mhbleakley/GF24/3D/NX2016SA_NDK.step

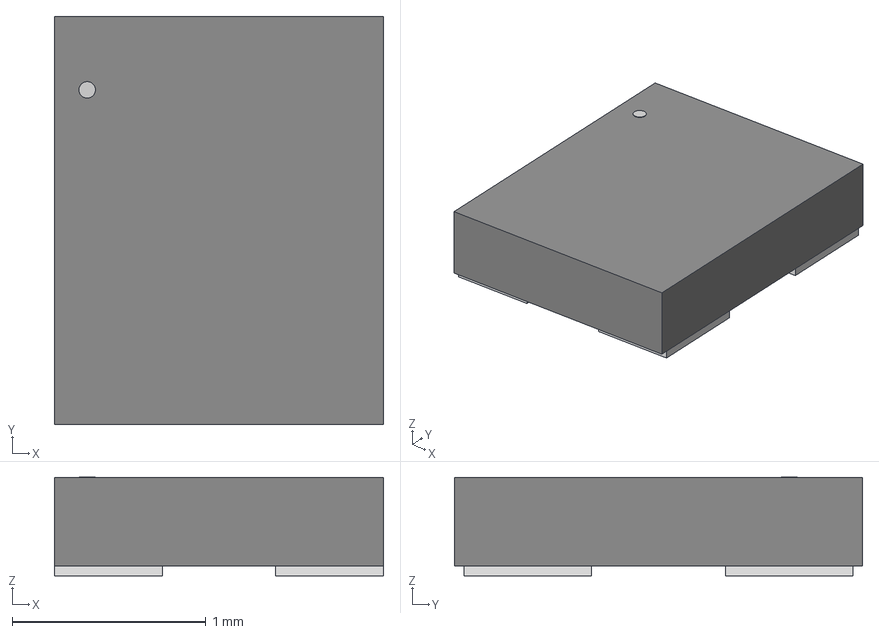
[picture p15: CAD file, 2025-01-12]
3D/NX2016SA_NDK.step
1.70 x 2.11 x 0.511 mm
