mhbleakley/GF24/3D/1101M2S5AQE2.stp

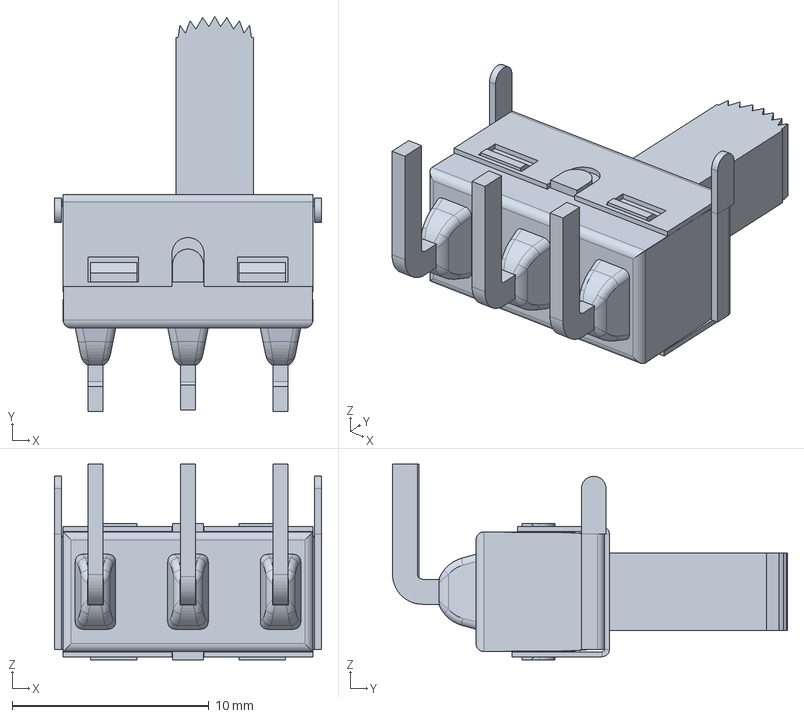
[picture p16: CAD file, 2025-01-12]
3D/1101M2S5AQE2.stp
13.6 x 20.1 x 9.93 mm
