mhbleakley/GF24/3D/3220-10-0100-00--3DModel-STEP-56544.STEP

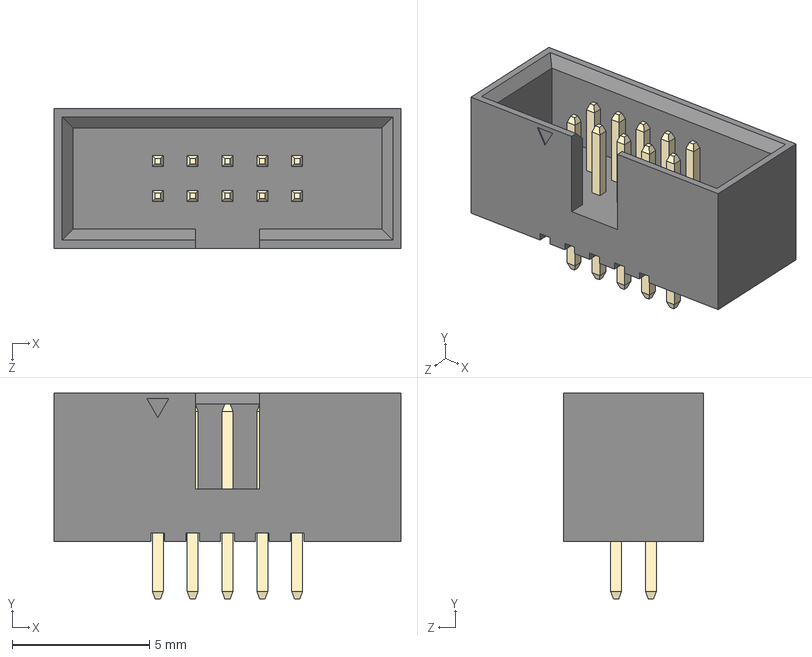
[picture p17: CAD file, 2025-01-12]
3D/3220-10-0100-00--3DModel-STEP-56544.STEP
12.7 x 7.50 x 5.10 mm
3220-xx-0100-00 body_10
Pin^3220-xx-0100-00 x 10
