mhbleakley/GF24/3D/PTS815SJM250SMTRLFS.stp

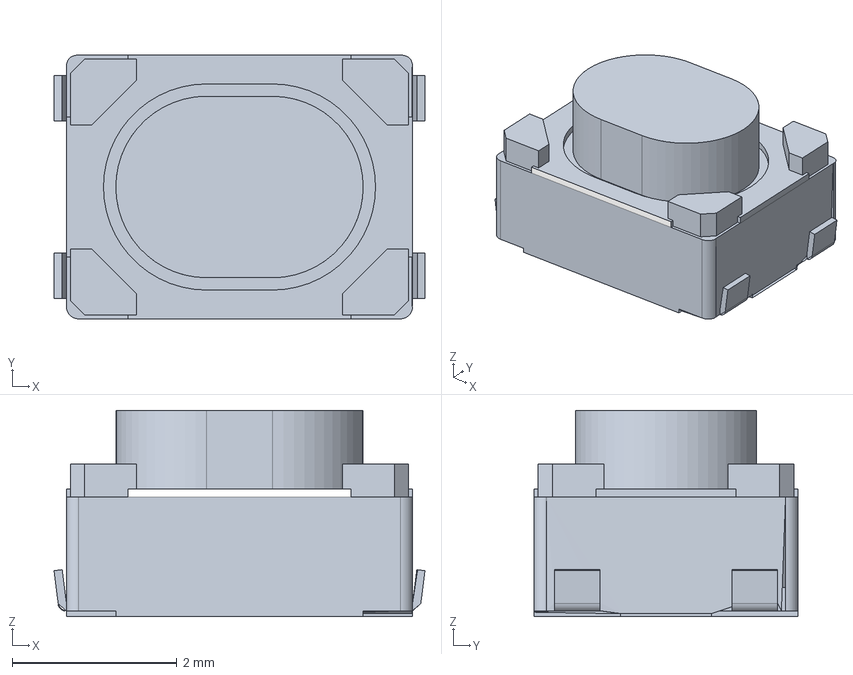
[picture p18: CAD file, 2025-01-12]
3D/PTS815SJM250SMTRLFS.stp
4.50 x 3.20 x 2.50 mm
PTS815SJM250SMTRLFS_PART1
PTS815SJM250SMTRLFS_PART2
PTS815SJM250SMTRLFS_PART3
