mhbleakley/GF24/3D/CJS-1200TA.step

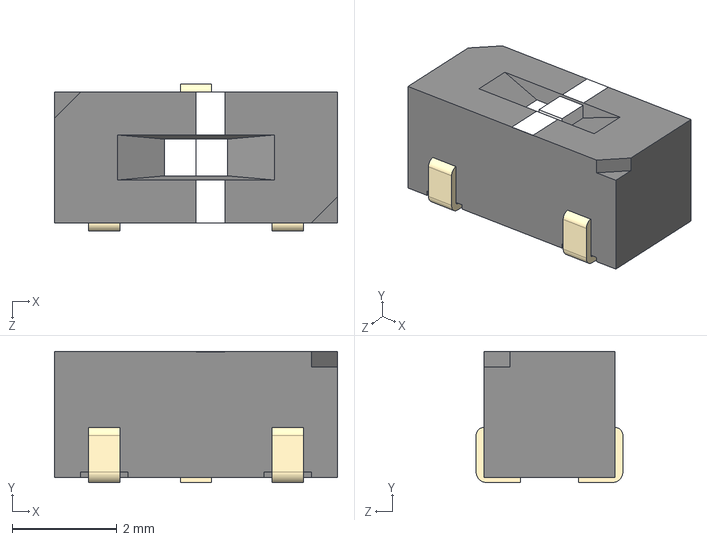
[picture p19: CAD file, 2025-01-12]
3D/CJS-1200TA.step
5.40 x 2.50 x 2.80 mm
