mhbleakley/GF24/3D/RC0603FR-0710KL.STEP

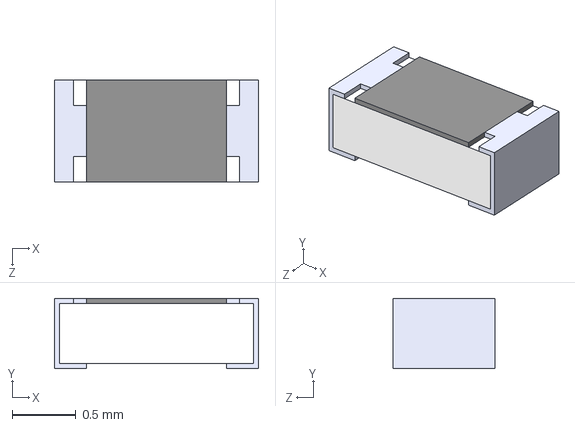
[picture p20: CAD file, 2025-01-12]
3D/RC0603FR-0710KL.STEP
1.60 x 0.55 x 0.8 mm
