mhbleakley/GF24/3D/SAM-M8Q-0.STEP

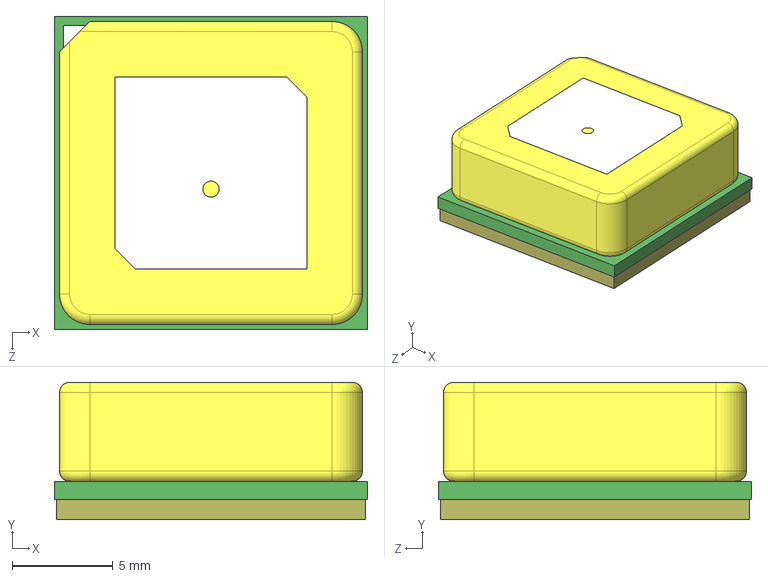
[picture p21: CAD file, 2025-01-12]
3D/SAM-M8Q-0.STEP
15.5 x 6.80 x 15.5 mm
