mhbleakley/GF24/3D/C0402C103K9RACTU.STEP

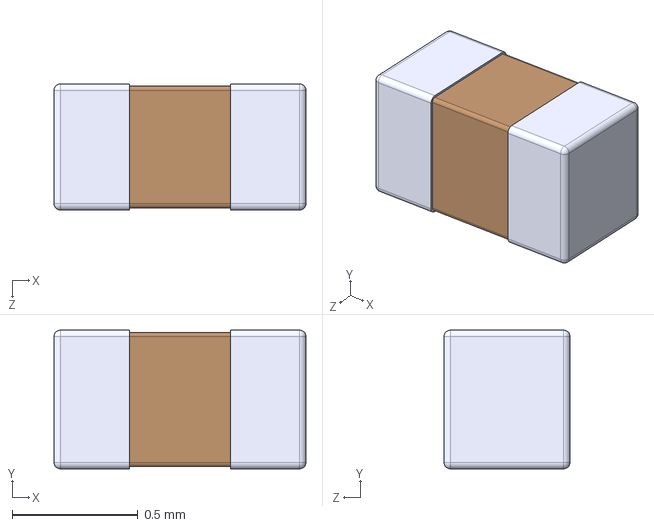
[picture p22: CAD file, 2025-01-12]
3D/C0402C103K9RACTU.STEP
1.00 x 0.55 x 0.5 mm
