mhbleakley/GF24/3D/MMSD4148T1G.STEP

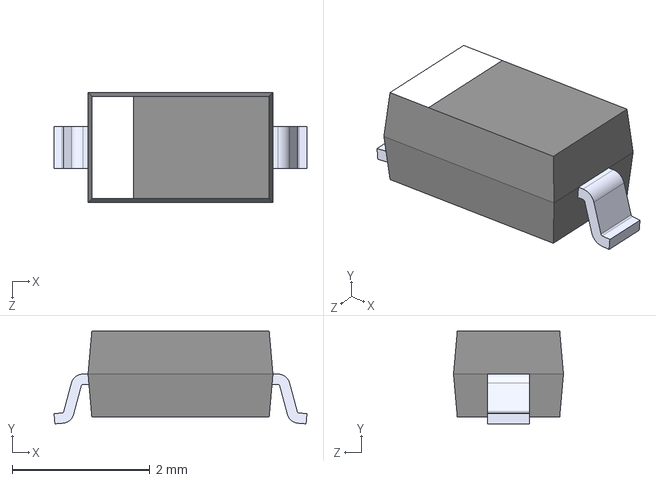
[picture p24: CAD file, 2025-01-12]
3D/MMSD4148T1G.STEP
3.68 x 1.35 x 1.60 mm
