mhbleakley/GF24/3D/CSQG703BP.step

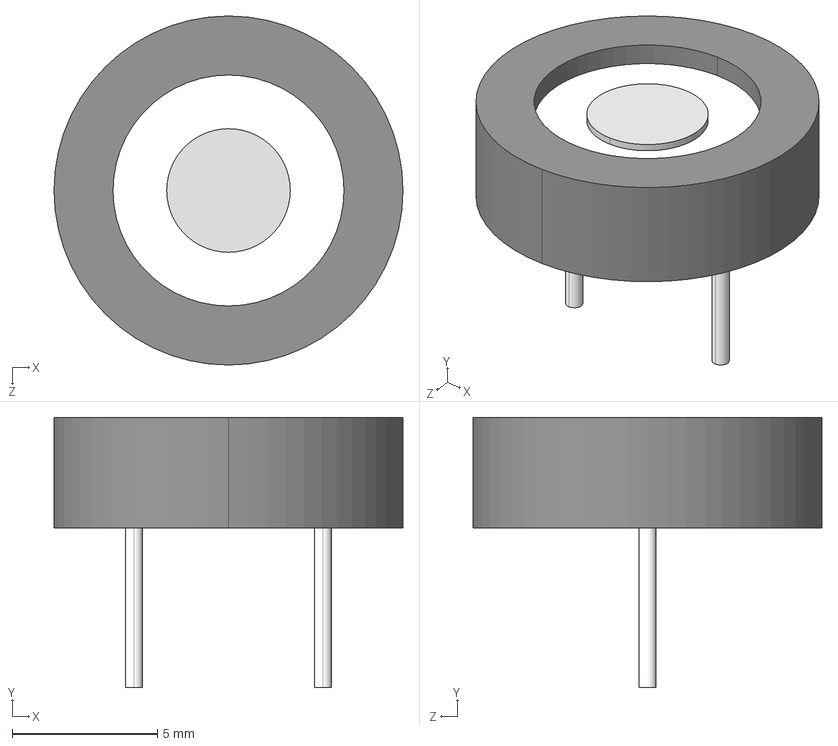
[picture p25: CAD file, 2025-01-12]
3D/CSQG703BP.step
12.0 x 9.30 x 12.0 mm
