mhbleakley/GF24/3D/APBDA3020.STEP

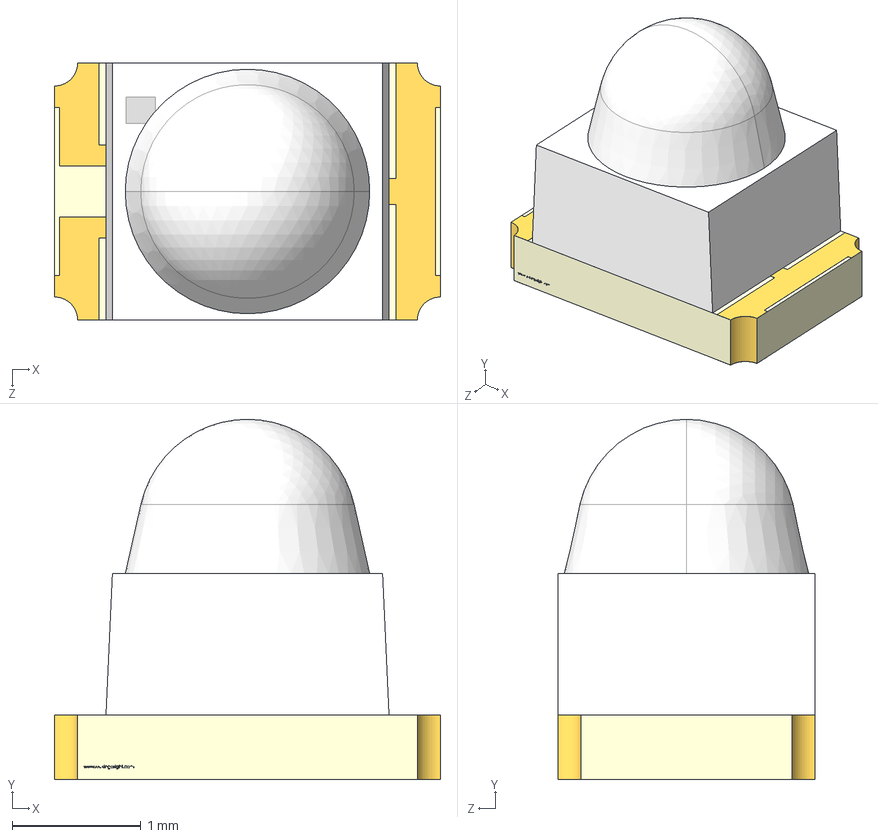
[picture p26: CAD file, 2025-01-12]
3D/APBDA3020.STEP
3.00 x 2.80 x 2.00 mm
