mhbleakley/GF24/3D/LM3671MF-3.3.step

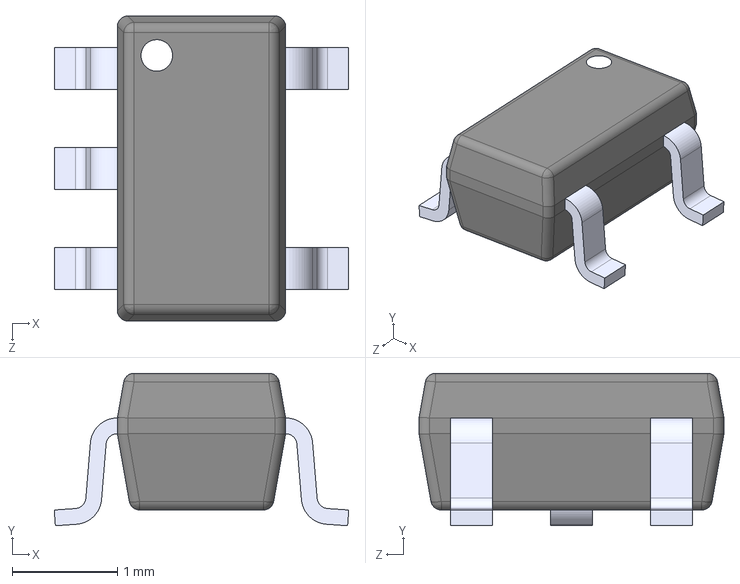
[picture p27: CAD file, 2024-12-28]
3D/LM3671MF-3.3.step
2.80 x 1.45 x 2.90 mm
