mhbleakley/GF24/3D/54.STEP

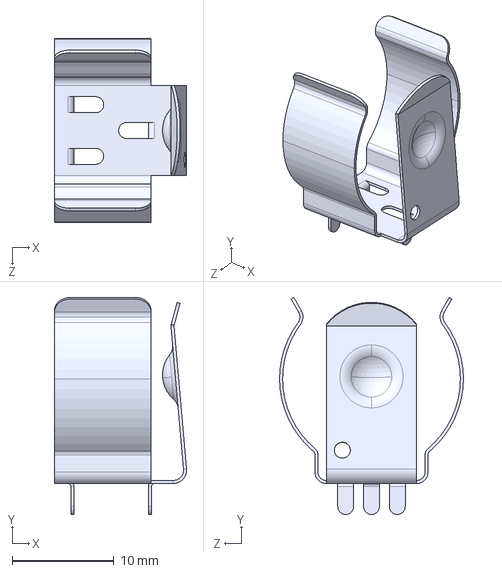
[picture p28: CAD file, 2024-12-27]
3D/54.STEP
13.0 x 21.4 x 18.1 mm
