mhbleakley/GF24/3D/C0603C103K9RACTU.STEP

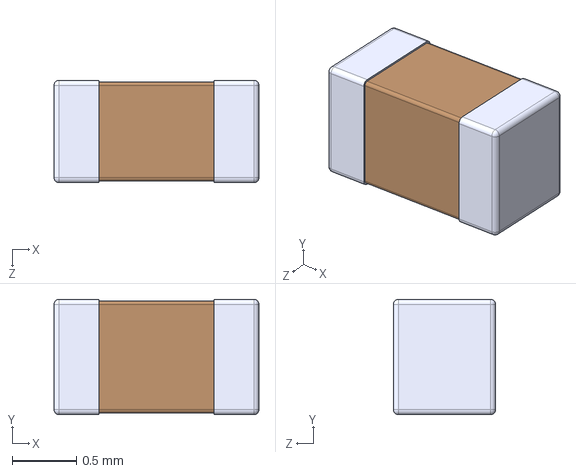
[picture p29: CAD file, 2024-12-27]
3D/C0603C103K9RACTU.STEP
1.60 x 0.9 x 0.8 mm
