mhbleakley/GF24/3D/C1206C475K9RACTU.step

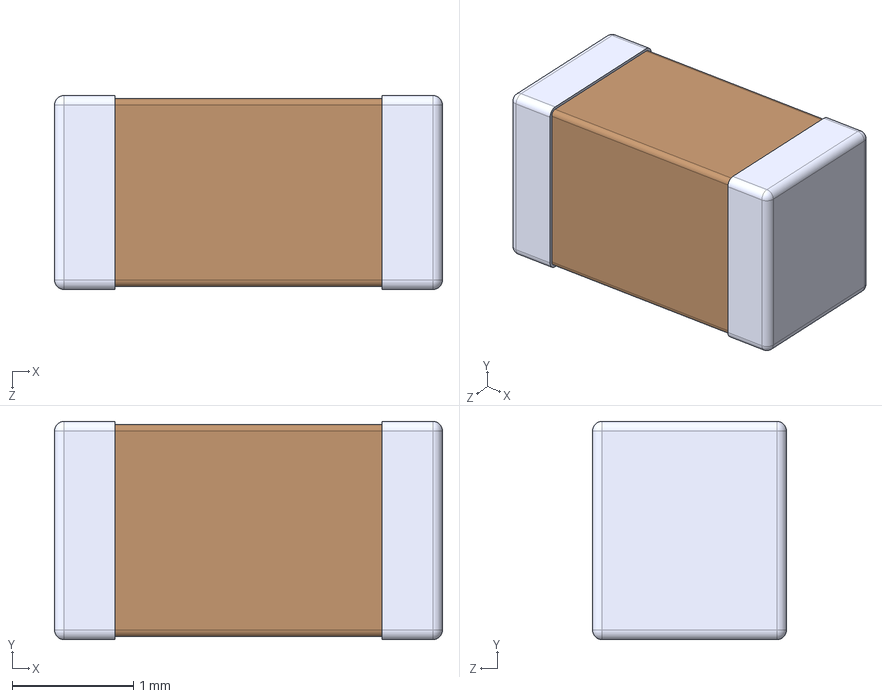
[picture p30: CAD file, 2024-12-27]
3D/C1206C475K9RACTU.step
3.20 x 1.80 x 1.60 mm
