mhbleakley/GF24/3D/RC1206JR-1010KL.step

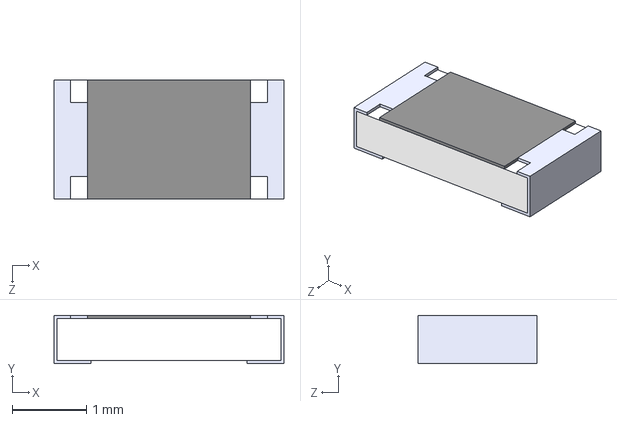
[picture p31: CAD file, 2024-12-27]
3D/RC1206JR-1010KL.step
3.10 x 0.65 x 1.60 mm
