mhbleakley/GF24/3D/C0805C104K9RACTU.step

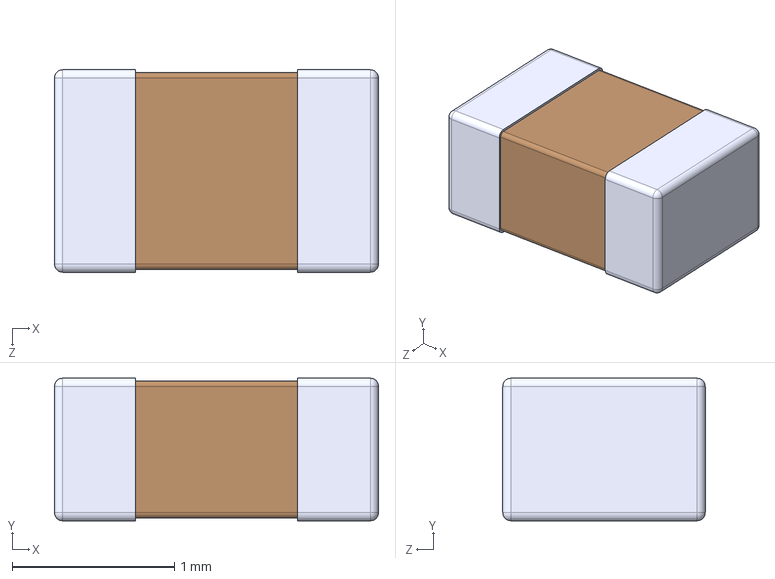
[picture p32: CAD file, 2024-12-27]
3D/C0805C104K9RACTU.step
2.00 x 0.88 x 1.25 mm
