mhbleakley/GF24/3D/ETQ-P3M2R2HFP.STEP

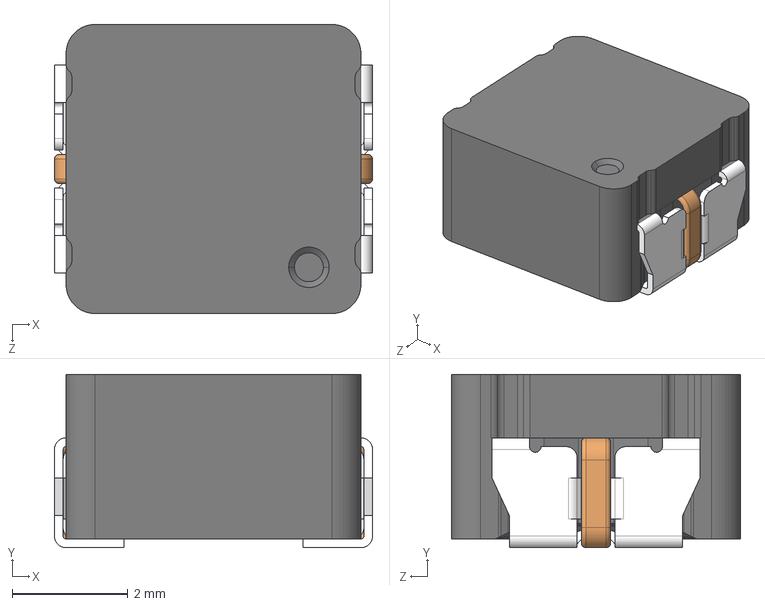
[picture p33: CAD file, 2024-12-27]
3D/ETQ-P3M2R2HFP.STEP
5.50 x 3.00 x 5.00 mm
