mhbleakley/GF24/3D/MAX-M10S-00B--3DModel-STEP-269445.STEP

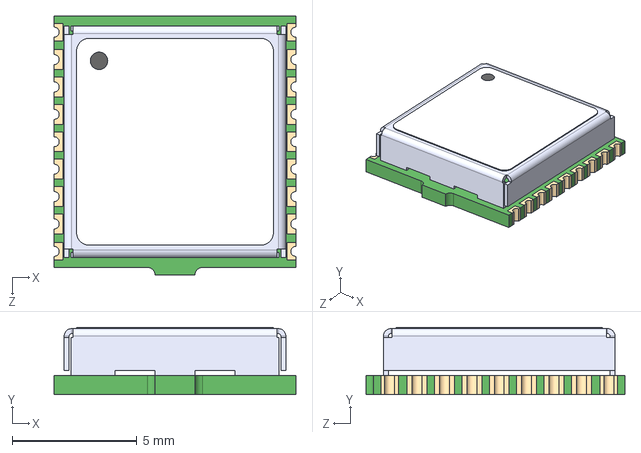
[picture p34: CAD file, 2024-12-27]
3D/MAX-M10S-00B--3DModel-STEP-269445.STEP
9.70 x 2.70 x 10.4 mm
